Kelsus/open-miyota-9075-gmt-case/output/print/print_case.3mf

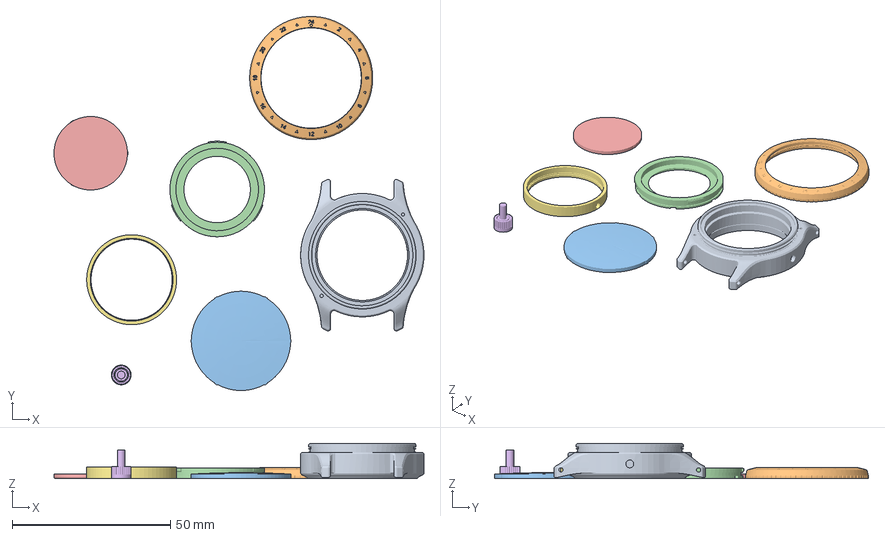
[picture p22: CAD file, 2026-08-03]
output/print/print_case.3mf
117.0 x 118.2 x 11.1 mm
p01_case.stl
p02_bezel.stl
p03_crystal.stl
p04_back.stl
p05_window.stl
p06_crown.stl
p08_movement_ring.stl
