Kelsus/open-miyota-9075-gmt-case/output/print/testprint.3mf

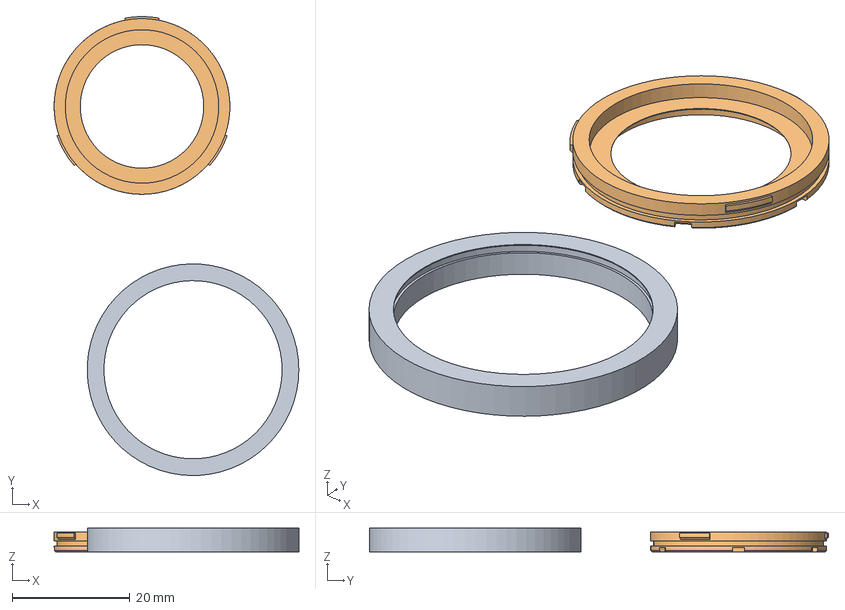
[picture p23: CAD file, 2026-08-03]
output/print/testprint.3mf
41.6 x 78.1 x 4.00 mm
p00_snap_coupon.stl
p04_back.stl
