Kelsus/open-miyota-9075-gmt-case/output/06_crown.step

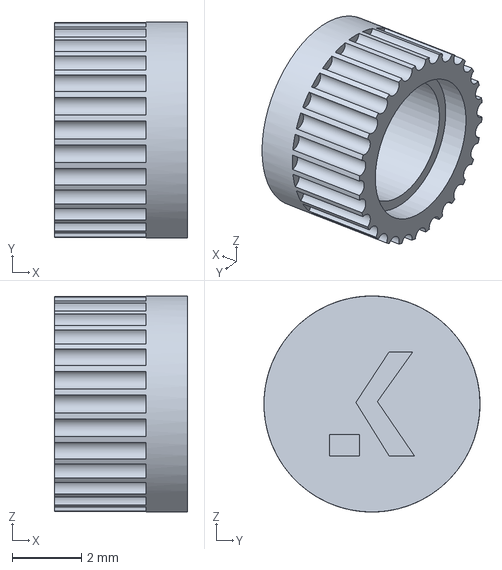
[picture p24: CAD file, 2026-08-14]
output/06_crown.step
3.85 x 6.25 x 6.25 mm
