Kelsus/open-miyota-9075-gmt-case/output/print/p05_window.stl

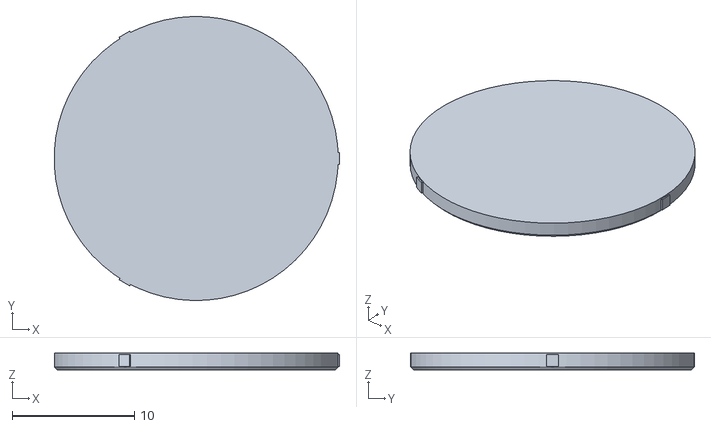
[picture p25: CAD file, 2026-08-03]
output/print/p05_window.stl
23.3 x 23.2 x 1.38
