Kelsus/open-miyota-9075-gmt-case/output/10_iring_gasket.step

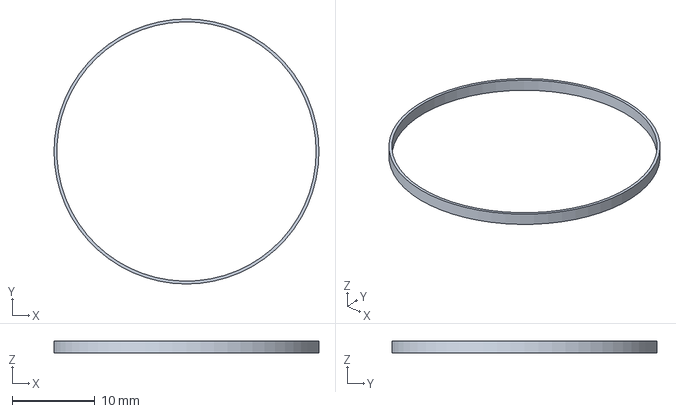
[picture p26: CAD file, 2026-08-14]
output/10_iring_gasket.step
32.1 x 32.1 x 1.40 mm
