Kelsus/open-miyota-9075-gmt-case/output/print/p03_crystal.stl

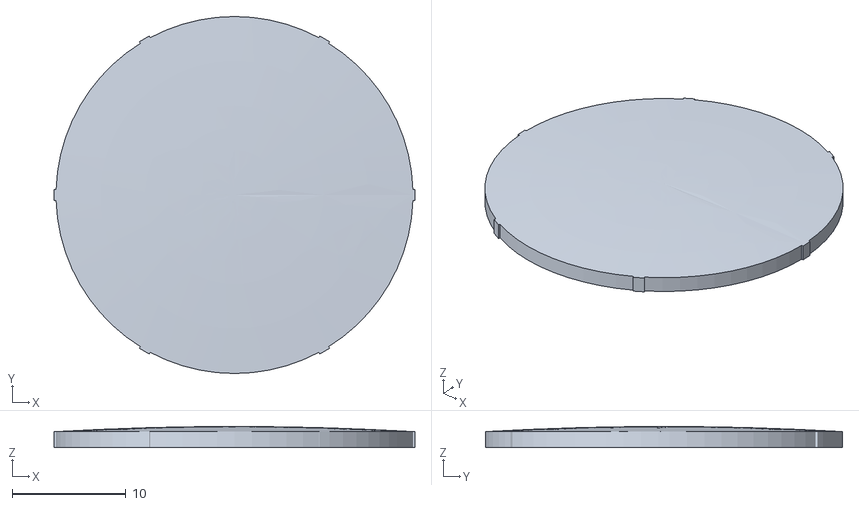
[picture p27: CAD file, 2026-08-03]
output/print/p03_crystal.stl
31.7 x 31.4 x 1.85
