Kelsus/open-miyota-9075-gmt-case/output/11_bezel_oring.step

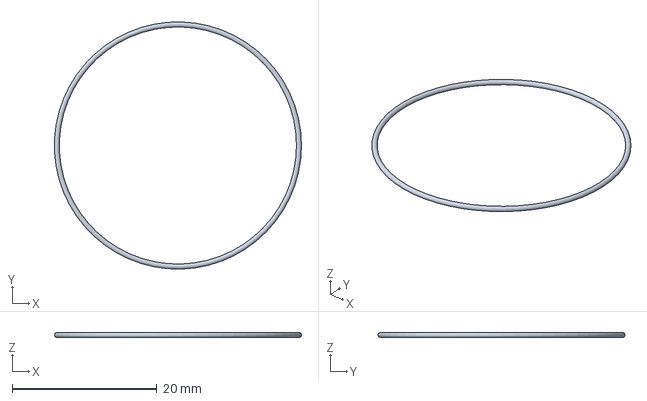
[picture p28: CAD file, 2026-08-14]
output/11_bezel_oring.step
34.2 x 34.2 x 0.7 mm
